mithro/rpi-camera-led/firmware/common/i2c_slave.h

/*
 * Single-File-Header for using the I2C peripheral in slave mode
 *
 * MIT License
 *
 * Copyright (c) 2024 Renze Nicolai
 *
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
 * Vendored from cnlohr/ch32v003fun's examples/i2c_slave/i2c_slave.h (the
 * ch32v003fun submodule pinned by this repository) so that
 * firmware/bootloader and firmware/app do not depend on the examples/
 * tree of the submodule, only on ch32fun/ch32fun.h itself.
 *
 * LOCAL MODIFICATIONS vs upstream (keep this list up to date):
 *
 *  1. The write callback is now only invoked for transactions that
 *     actually wrote register data. Upstream calls it from the STOPF
 *     branch unconditionally, so a *master read* (which also ends in a
 *     STOP, with position advanced past offset) is reported to the
 *     application as if it were a register write of the same length.
 *     For this firmware that is not cosmetic: the bootloader's
 *     "was BREG_CMD written?" test would re-execute a stale command
 *     just because a host read a block spanning register 0x03, and the
 *     app's REG_BOOT test would likewise fire on a pure read.
 *     `i2c_slave_state.writing` already tracked this upstream but was
 *     never used; it is now the gate.
 *
 *  2. A write phase terminated by a repeated START (the combined
 *     write-then-read that regmap-i2c / i2cget -c / I2C_RDWR issue) now
 *     flushes the write callback from the ADDR branch, before offset /
 *     position are reset for the read phase. Upstream silently dropped
 *     the write callback in that case.
 *
 *  3. The error interrupt handler clears *every* error flag that
 *     I2C_CTLR2_ITERREN can raise, not just BERR/ARLO/AF. Upstream
 *     leaves OVR/PECERR/TIMEOUT/SMBALERT set, and because the handler
 *     then returns with the interrupt condition still asserted the CPU
 *     re-enters it forever -- a permanent lockup of the main loop,
 *     which for the bootloader means a hung firmware upgrade.
 */

#ifndef __I2C_SLAVE_H
#define __I2C_SLAVE_H

#include "ch32fun.h"
#include <stdint.h>
#include <stdio.h>
#include <stdbool.h>

typedef void (*i2c_write_callback_t)(uint8_t reg, uint8_t length);
typedef void (*i2c_read_callback_t)(uint8_t reg);

struct _i2c_slave_state {
    uint8_t first_write;
    uint8_t offset;
    uint8_t position;
    volatile uint8_t* volatile registers1;
    volatile uint8_t size1;
    volatile uint8_t* volatile registers2;
    volatile uint8_t size2;
    i2c_write_callback_t write_callback1;
    i2c_read_callback_t read_callback1;
    bool read_only1;
    i2c_write_callback_t write_callback2;
    i2c_read_callback_t read_callback2;
    bool read_only2;
    bool writing;
    bool address2matched;
} i2c_slave_state;

void SetupI2CSlave(uint8_t address, volatile uint8_t* registers, uint8_t size, i2c_write_callback_t write_callback, i2c_read_callback_t read_callback, bool read_only) {
    i2c_slave_state.first_write = 1;
    i2c_slave_state.offset = 0;
    i2c_slave_state.position = 0;
    i2c_slave_state.registers1 = registers;
    i2c_slave_state.size1 = size;
    i2c_slave_state.registers2 = NULL;
    i2c_slave_state.size2 = 0;
    i2c_slave_state.write_callback1 = write_callback;
    i2c_slave_state.read_callback1 = read_callback;
    i2c_slave_state.read_only1 = read_only;
    i2c_slave_state.write_callback2 = NULL;
    i2c_slave_state.read_callback2 = NULL;
    i2c_slave_state.read_only2 = false;

    // Enable I2C1
    RCC->APB1PCENR |= RCC_APB1Periph_I2C1;

    // Reset I2C1 to init all regs
    RCC->APB1PRSTR |= RCC_APB1Periph_I2C1;
    RCC->APB1PRSTR &= ~RCC_APB1Periph_I2C1;

    I2C1->CTLR1 |= I2C_CTLR1_SWRST;
    I2C1->CTLR1 &= ~I2C_CTLR1_SWRST;

    // Set module clock frequency
    uint32_t prerate = 2000000; // I2C Logic clock rate, must be higher than the bus clock rate
    I2C1->CTLR2 |= (FUNCONF_SYSTEM_CORE_CLOCK/prerate) & I2C_CTLR2_FREQ;

    // Enable interrupts
    I2C1->CTLR2 |= I2C_CTLR2_ITBUFEN | I2C_CTLR2_ITEVTEN | I2C_CTLR2_ITERREN;

    NVIC_EnableIRQ(I2C1_EV_IRQn); // Event interrupt
    NVIC_SetPriority(I2C1_EV_IRQn, 2 << 4);
    NVIC_EnableIRQ(I2C1_ER_IRQn); // Error interrupt
    NVIC_SetPriority(I2C1_ER_IRQn, 2 << 4);

    // Set clock configuration
    uint32_t clockrate = 1000000; // I2C Bus clock rate, must be lower than the logic clock rate
    I2C1->CKCFGR = ((FUNCONF_SYSTEM_CORE_CLOCK/(3*clockrate))&I2C_CKCFGR_CCR) | I2C_CKCFGR_FS; // Fast mode 33% duty cycle
    //I2C1->CKCFGR = ((FUNCONF_SYSTEM_CORE_CLOCK/(25*clockrate))&I2C_CKCFGR_CCR) | I2C_CKCFGR_DUTY | I2C_CKCFGR_FS; // Fast mode 36% duty cycle
    //I2C1->CKCFGR = (FUNCONF_SYSTEM_CORE_CLOCK/(2*clockrate))&I2C_CKCFGR_CCR; // Standard mode good to 100kHz

    // Set I2C address
    I2C1->OADDR1 = address << 1;
    I2C1->OADDR2 = 0;

    // Enable I2C
    I2C1->CTLR1 |= I2C_CTLR1_PE;

    // Acknowledge bytes when they are received
    I2C1->CTLR1 |= I2C_CTLR1_ACK;
}

void SetupSecondaryI2CSlave(uint8_t address, volatile uint8_t* registers, uint8_t size, i2c_write_callback_t write_callback, i2c_read_callback_t read_callback, bool read_only) {
    if (address > 0) {
        I2C1->OADDR2 = (address << 1) | 1;
        i2c_slave_state.registers2 = registers;
        i2c_slave_state.size2 = size;
        i2c_slave_state.write_callback2 = write_callback;
        i2c_slave_state.read_callback2 = read_callback;
        i2c_slave_state.read_only2 = read_only;
    } else {
        I2C1->OADDR2 = 0;
    }
}

void SetI2CSlaveReadOnly(bool read_only) {
    i2c_slave_state.read_only1 = read_only;
}

void SetSecondaryI2CSlaveReadOnly(bool read_only) {
    i2c_slave_state.read_only2 = read_only;
}

/* Deliver the write callback for a completed write phase, if the
 * transaction actually carried register data (as opposed to a bare
 * pointer-set write, or a master read). Called both on STOP and on a
 * repeated START, since a combined write-then-read transfer ends its
 * write phase with the latter. */
static void i2c_slave_flush_write(void) {
    if (!i2c_slave_state.writing)
        return;
    i2c_slave_state.writing = false;
    uint8_t reg = i2c_slave_state.offset;
    uint8_t len = (uint8_t)(i2c_slave_state.position - i2c_slave_state.offset);
    if (i2c_slave_state.address2matched) {
        if (i2c_slave_state.write_callback2 != NULL)
            i2c_slave_state.write_callback2(reg, len);
    } else {
        if (i2c_slave_state.write_callback1 != NULL)
            i2c_slave_state.write_callback1(reg, len);
    }
}

void I2C1_EV_IRQHandler(void) __attribute__((interrupt));
void I2C1_EV_IRQHandler(void) {
    uint16_t STAR1, STAR2 __attribute__((unused));
    STAR1 = I2C1->STAR1;
    STAR2 = I2C1->STAR2;

    if (STAR1 & I2C_STAR1_ADDR) { // Start event
        /* A repeated START ends any write phase that was in progress;
         * report it before offset/position are reset below. */
        i2c_slave_flush_write();
        i2c_slave_state.first_write = 1; // Next write will be the offset
        i2c_slave_state.position = i2c_slave_state.offset; // Reset position
        i2c_slave_state.address2matched = !!(STAR2 & I2C_STAR2_DUALF);
    }

    if (STAR1 & I2C_STAR1_RXNE) { // Write event
        if (i2c_slave_state.first_write) { // First byte written, set the offset
            i2c_slave_state.offset = I2C1->DATAR;
            i2c_slave_state.position = i2c_slave_state.offset;
            i2c_slave_state.first_write = 0;
            i2c_slave_state.writing = false;
        } else { // Normal register write
            i2c_slave_state.writing = true;
            if (i2c_slave_state.address2matched) {
                if (i2c_slave_state.position < i2c_slave_state.size2 && !i2c_slave_state.read_only2) {
                    i2c_slave_state.registers2[i2c_slave_state.position] = I2C1->DATAR;
                    i2c_slave_state.position++;
                }
            } else {
                if (i2c_slave_state.position < i2c_slave_state.size1 && !i2c_slave_state.read_only1) {
                    i2c_slave_state.registers1[i2c_slave_state.position] = I2C1->DATAR;
                    i2c_slave_state.position++;
                }
            }
        }
    }

    if (STAR1 & I2C_STAR1_TXE) { // Read event
        i2c_slave_state.writing = false;
        if (i2c_slave_state.address2matched) {
            if (i2c_slave_state.position < i2c_slave_state.size2) {
                I2C1->DATAR = i2c_slave_state.registers2[i2c_slave_state.position];
                if (i2c_slave_state.read_callback2 != NULL) {
                    i2c_slave_state.read_callback2(i2c_slave_state.position);
                }
                i2c_slave_state.position++;
            } else {
                I2C1->DATAR = 0x00;
            }
        } else {
            if (i2c_slave_state.position < i2c_slave_state.size1) {
                I2C1->DATAR = i2c_slave_state.registers1[i2c_slave_state.position];
                if (i2c_slave_state.read_callback1 != NULL) {
                    i2c_slave_state.read_callback1(i2c_slave_state.position);
                }
                i2c_slave_state.position++;
            } else {
                I2C1->DATAR = 0x00;
            }
        }
    }

    if (STAR1 & I2C_STAR1_STOPF) { // Stop event
        // STOPF is cleared by a read of STAR1 (done above) followed by a
        // write to CTLR1; this read-modify-write is that write.
        I2C1->CTLR1 &= ~(I2C_CTLR1_STOP); // Clear stop
        i2c_slave_flush_write();
    }
}

/* Every error condition I2C_CTLR2_ITERREN can raise. All of these are
 * rc_w0: writing the register back with the bit cleared clears it, and
 * writing 1 to any other flag is ignored, so one store clears the lot. */
#define I2C_SLAVE_ERR_FLAGS (I2C_STAR1_BERR | I2C_STAR1_ARLO | I2C_STAR1_AF | \
                             I2C_STAR1_OVR | I2C_STAR1_PECERR)

void I2C1_ER_IRQHandler(void) __attribute__((interrupt));
void I2C1_ER_IRQHandler(void) {
    uint16_t STAR1 = I2C1->STAR1;

    /* Clear *all* pending error flags unconditionally. Leaving any one
     * of them set (upstream ignores OVR and PECERR entirely) leaves the
     * error interrupt permanently asserted, which re-enters this
     * handler forever and starves the main loop. */
    if (STAR1 & I2C_SLAVE_ERR_FLAGS) {
        I2C1->STAR1 = (uint16_t)(STAR1 & ~I2C_SLAVE_ERR_FLAGS);
    }
}

#endif
