mithro/rpi-camera-led/firmware/common/app_header.h

/*
 * The 16-byte trailer written into the last 16 bytes of the app flash
 * region (see layout.h, APP_HEADER_ADDR / APP_HEADER_PAGE_INDEX).
 * Used by the bootloader to decide whether the flashed application is
 * safe to run, and by the host-side upgrade tool to build a correct
 * final page.
 */
#ifndef FIRMWARE_COMMON_APP_HEADER_H
#define FIRMWARE_COMMON_APP_HEADER_H

#include <stdint.h>

typedef struct {
    uint32_t magic;          /* must equal APP_HEADER_MAGIC */
    uint32_t app_used_size;  /* bytes of real app image, from APP_FLASH_BASE,
                               * INCLUDING this header. Because the header
                               * sits at the fixed offset APP_HEADER_OFFSET
                               * and APP_HEADER_OFFSET + APP_HEADER_SIZE ==
                               * APP_SIZE, the only self-consistent value is
                               * APP_SIZE; both bootloader.c's verify_app()
                               * and host/app_trailer.py reject anything
                               * else. CRC32 below covers exactly this many
                               * bytes. */
    uint32_t app_crc32;      /* CRC-32/ISO-HDLC, i.e. exactly what Python's
                               * zlib.crc32() returns (poly 0xEDB88320,
                               * reflected, init 0xFFFFFFFF, final XOR
                               * 0xFFFFFFFF -- see crc32.h), over the
                               * app_used_size bytes starting at
                               * APP_FLASH_BASE, computed with THIS FIELD
                               * treated as zero during the calculation. */
    uint32_t reserved;       /* must be 0, reserved for future use */
} app_header_t;

#endif /* FIRMWARE_COMMON_APP_HEADER_H */
